martrewes/CompleteLightsOutProject/ArduinoCode/src/levels.h

char Level1[25] = {'0', '0', '0', '0', '0', '0', '0', '0', '0', '0', '0', '0', '0', '0', '0', '1', '0', '1', '0', '1', '1', '0', '1', '0', '1'};
char Level2[25] = {'1', '0', '1', '0', '1', '1', '0', '1', '0', '1', '0', '0', '0', '0', '0', '1', '0', '1', '0', '1', '1', '0', '1', '0', '1'};
char Level3[25] = {'0', '1', '0', '1', '0', '1', '1', '0', '1', '1', '1', '1', '0', '1', '1', '1', '1', '0', '1', '1', '0', '1', '0', '1', '0'};
char Level4[25] = {'0', '0', '0', '0', '0', '1', '1', '0', '1', '1', '0', '0', '0', '0', '0', '1', '0', '0', '0', '1', '1', '1', '0', '1', '1'};
char Level5[25] = {'1', '1', '1', '1', '0', '1', '1', '1', '0', '1', '1', '1', '1', '0', '1', '0', '0', '0', '1', '1', '1', '1', '0', '1', '1'};
char Level6[25] = {'0', '0', '0', '0', '0', '0', '0', '0', '0', '0', '1', '0', '1', '0', '1', '1', '0', '1', '0', '1', '0', '1', '1', '1', '0'};
char Level7[25] = {'1', '1', '1', '1', '0', '1', '0', '0', '0', '1', '1', '0', '0', '0', '1', '1', '0', '0', '0', '1', '1', '1', '1', '1', '0'};
char Level8[25] = {'0', '0', '0', '0', '0', '0', '0', '1', '0', '0', '0', '1', '0', '1', '0', '1', '0', '1', '0', '1', '0', '1', '0', '1', '0'};
char Level9[25] = {'0', '1', '0', '1', '0', '1', '1', '1', '1', '1', '0', '1', '1', '1', '0', '0', '1', '0', '1', '1', '1', '1', '1', '0', '0'};
char Level10[25] = {'0', '1', '1', '1', '0', '0', '1', '1', '1', '0', '0', '1', '1', '1', '0', '0', '0', '0', '0', '0', '0', '0', '0', '0', '0'};
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
char HLevel29[25] = {'2', '1', '2', '0', '0', '2', '2', '2', '1', '0', '1', '0', '2', '0', '1', '0', '1', '2', '2', '2', '0', '0', '2', '1', '2'};
char HLevel30[25] = {'0', '0', '2', '0', '0', '1', '0', '1', '0', '1', '2', '1', '2', '1', '2', '1', '0', '1', '0', '1', '0', '0', '2', '0', '0'};
char HLevel31[25] = {'0', '2', '0', '0', '2', '2', '2', '1', '1', '0', '0', '1', '1', '1', '0', '0', '1', '1', '2', '2', '2', '0', '0', '2', '0'};
char HLevel32[25] = {'0', '1', '1', '1', '0', '0', '0', '0', '0', '0', '2', '0', '2', '0', '2', '0', '0', '0', '0', '0', '2', '0', '2', '0', '2'};
char HLevel33[25] = {'0', '1', '1', '1', '0', '0', '0', '0', '0', '0', '1', '0', '0', '0', '1', '0', '0', '0', '0', '0', '2', '0', '2', '0', '2'};
char HLevel34[25] = {'0', '2', '1', '2', '2', '0', '2', '2', '1', '2', '0', '1', '0', '0', '2', '0', '0', '0', '1', '2', '0', '0', '2', '1', '2'};
char HLevel35[25] = {'1', '2', '0', '2', '1', '1', '2', '0', '2', '1', '1', '2', '1', '2', '1', '1', '2', '0', '2', '1', '1', '2', '0', '2', '1'};
char HLevel36[25] = {'0', '0', '0', '0', '0', '1', '0', '2', '0', '1', '1', '0', '1', '0', '1', '1', '0', '2', '0', '1', '0', '0', '0', '0', '0'};
char HLevel37[25] = {'2', '2', '0', '2', '2', '0', '1', '2', '0', '0', '0', '2', '1', '1', '2', '2', '2', '1', '1', '2', '0', '2', '0', '2', '0'};
char HLevel38[25] = {'2', '1', '2', '0', '0', '2', '2', '1', '1', '0', '1', '2', '1', '2', '1', '0', '1', '1', '2', '2', '0', '0', '2', '1', '2'};
char HLevel39[25] = {'0', '0', '1', '0', '0', '0', '0', '1', '0', '0', '0', '0', '0', '0', '0', '0', '0', '2', '0', '0', '0', '0', '2', '0', '0'};
char HLevel40[25] = {'0', '0', '1', '0', '0', '0', '1', '1', '1', '0', '2', '2', '2', '2', '2', '1', '2', '2', '2', '1', '1', '1', '2', '1', '1'};
char HLevel41[25] = {'1', '0', '2', '0', '1', '0', '0', '0', '0', '0', '2', '0', '1', '0', '2', '0', '0', '0', '0', '0', '1', '0', '2', '0', '1'};
char HLevel42[25] = {'2', '0', '1', '0', '2', '0', '0', '2', '0', '0', '1', '2', '1', '2', '1', '0', '0', '2', '0', '0', '2', '0', '1', '0', '2'};
char HLevel43[25] = {'0', '0', '0', '0', '0', '0', '2', '0', '0', '0', '0', '0', '2', '0', '0', '0', '2', '0', '0', '0', '0', '0', '0', '0', '0'};
char HLevel44[25] = {'1', '1', '1', '2', '1', '1', '1', '1', '0', '1', '1', '0', '1', '1', '0', '1', '2', '2', '0', '1', '2', '0', '0', '0', '1'};
char HLevel45[25] = {'2', '2', '1', '2', '1', '1', '2', '2', '0', '1', '2', '1', '2', '2', '0', '2', '2', '1', '0', '1', '2', '2', '2', '0', '1'};
char HLevel46[25] = {'2', '1', '1', '1', '2', '1', '2', '1', '2', '1', '1', '1', '2', '1', '1', '1', '2', '1', '2', '1', '2', '1', '1', '1', '2'};
char HLevel47[25] = {'0', '0', '2', '0', '0', '0', '2', '2', '1', '0', '0', '0', '0', '2', '2', '2', '1', '2', '0', '2', '1', '1', '0', '1', '1'};
char HLevel48[25] = {'0', '0', '0', '0', '0', '1', '0', '2', '0', '1', '2', '0', '2', '0', '2', '1', '0', '2', '0', '1', '0', '0', '0', '0', '0'};
char HLevel49[25] = {'0', '2', '0', '0', '0', '0', '2', '0', '0', '0', '0', '0', '1', '0', '0', '0', '0', '0', '2', '2', '2', '0', '0', '0', '0'};
char HLevel50[25] = {'0', '2', '2', '2', '0', '0', '2', '1', '2', '0', '0', '2', '2', '2', '0', '0', '2', '2', '2', '0', '0', '0', '0', '0', '0'};

char XHLevel1[25] = {'0', '0', '2', '0', '0', '1', '0', '0', '0', '1', '1', '0', '2', '0', '1', '1', '0', '0', '0', '1', '0', '0', '2', '0', '0'};
char XHLevel2[25] = {'2', '0', '2', '0', '2', '0', '0', '0', '0', '0', '2', '0', '1', '0', '2', '0', '0', '0', '0', '0', '2', '0', '2', '0', '2'};
char XHLevel3[25] = {'0', '2', '2', '2', '0', '0', '2', '2', '2', '0', '2', '1', '1', '1', '2', '2', '1', '1', '1', '2', '2', '1', '1', '1', '2'};
char XHLevel4[25] = {'1', '0', '0', '0', '1', '2', '0', '0', '0', '2', '2', '0', '0', '0', '2', '2', '0', '0', '0', '2', '1', '0', '0', '0', '1'};
char XHLevel5[25] = {'0', '1', '0', '1', '0', '0', '0', '0', '0', '0', '1', '0', '0', '0', '1', '0', '2', '2', '2', '0', '0', '0', '2', '0', '0'};
char XHLevel6[25] = {'2', '0', '2', '0', '2', '0', '0', '0', '0', '0', '2', '0', '2', '0', '2', '0', '0', '0', '0', '0', '2', '0', '2', '0', '2'};
char XHLevel7[25] = {'2', '1', '1', '1', '2', '2', '1', '1', '1', '2', '2', '1', '1', '1', '2', '2', '1', '1', '1', '2', '2', '1', '1', '1', '2'};
char XHLevel8[25] = {'0', '0', '0', '0', '0', '0', '0', '0', '0', '0', '0', '2', '1', '2', '0', '0', '0', '0', '0', '0', '0', '0', '0', '0', '0'};
char XHLevel9[25] = {'0', '0', '2', '0', '0', '1', '1', '0', '1', '1', '0', '0', '0', '0', '0', '0', '0', '2', '0', '0', '0', '0', '0', '0', '0'};
char XHLevel10[25] = {'0', '0', '0', '0', '0', '0', '0', '0', '0', '0', '1', '0', '0', '0', '1', '0', '0', '0', '0', '0', '0', '0', '0', '0', '0'};
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
char XHLevel39[25] = {'1', '0', '1', '0', '1', '0', '1', '1', '1', '0', '0', '0', '2', '0', '0', '0', '0', '0', '0', '0', '1', '0', '0', '0', '1'};
char XHLevel40[25] = {'1', '1', '0', '2', '2', '1', '1', '0', '2', '2', '1', '1', '1', '1', '1', '1', '1', '1', '2', '2', '1', '1', '1', '2', '2'};
char XHLevel41[25] = {'0', '0', '0', '0', '0', '1', '0', '0', '0', '1', '1', '0', '0', '0', '1', '1', '0', '0', '0', '1', '0', '0', '0', '0', '0'};
char XHLevel42[25] = {'1', '1', '1', '0', '0', '1', '0', '0', '0', '0', '1', '1', '0', '0', '0', '1', '0', '0', '0', '0', '1', '1', '1', '0', '0'};
char XHLevel43[25] = {'2', '1', '2', '1', '2', '1', '2', '1', '2', '1', '2', '1', '0', '1', '2', '1', '2', '1', '2', '1', '2', '1', '2', '1', '2'};
char XHLevel44[25] = {'1', '2', '2', '2', '1', '2', '0', '2', '1', '1', '2', '0', '0', '2', '1', '1', '2', '1', '1', '2', '2', '2', '0', '2', '2'};
char XHLevel45[25] = {'1', '2', '1', '2', '1', '1', '0', '1', '0', '1', '1', '0', '1', '0', '1', '1', '1', '1', '1', '1', '1', '0', '1', '0', '1'};
char XHLevel46[25] = {'0', '0', '1', '1', '1', '0', '0', '2', '0', '2', '2', '1', '2', '2', '0', '0', '1', '2', '0', '1', '0', '1', '0', '0', '2'};
char XHLevel47[25] = {'1', '1', '2', '0', '0', '0', '1', '2', '2', '1', '1', '0', '0', '0', '1', '2', '2', '0', '2', '1', '1', '2', '1', '1', '0'};
char XHLevel48[25] = {'1', '0', '1', '0', '0', '1', '0', '0', '1', '0', '2', '2', '1', '2', '0', '1', '0', '0', '2', '1', '2', '2', '1', '1', '0'};
char XHLevel49[25] = {'1', '1', '2', '1', '1', '0', '1', '2', '1', '0', '1', '0', '2', '0', '1', '0', '1', '1', '1', '0', '1', '0', '1', '0', '1'};
char XHLevel50[25] = {'2', '0', '1', '0', '2', '1', '2', '1', '2', '1', '1', '0', '2', '0', '1', '0', '0', '0', '0', '0', '1', '0', '0', '0', '1'};

char menuLeds[25] = {'0', '1', '0', '1', '0', '1', '0', '0', '0', '1', '0', '1', '0', '1', '0', '0', '0', '0', '0', '0', '0', '2', '2', '2', '0'};

// 'bg', 128x32px
const unsigned char bgImage [] PROGMEM = {
    0xff, 0xff, 0xff, 0xff, 0xff, 0xff, 0xff, 0xff, 0xff, 0xff, 0xff, 0xff, 0xff, 0xff, 0xff, 0xff, 
    0x80, 0x00, 0x00, 0x00, 0x00, 0x00, 0x00, 0x00, 0xc0, 0x00, 0x00, 0x00, 0x00, 0x00, 0x00, 0x01, 
    0xa0, 0x00, 0x04, 0x00, 0x00, 0x00, 0x00, 0x00, 0xd1, 0x00, 0x00, 0x00, 0x00, 0x00, 0x00, 0x01, 
    0xa1, 0x92, 0x64, 0x00, 0x00, 0x00, 0x00, 0x00, 0xdb, 0x32, 0x4c, 0x70, 0x00, 0x00, 0x00, 0x01, 
    0xa2, 0xd2, 0xb4, 0x00, 0x00, 0x00, 0x00, 0x00, 0xd5, 0x4a, 0x56, 0xc0, 0x00, 0x00, 0x00, 0x01, 
    0xa3, 0x14, 0xc4, 0x00, 0x00, 0x00, 0x00, 0x00, 0xd1, 0x4a, 0x98, 0x30, 0x00, 0x00, 0x00, 0x01, 
    0xb9, 0x88, 0x64, 0x00, 0x00, 0x00, 0x00, 0x00, 0xd1, 0x31, 0x0c, 0xe0, 0x00, 0x00, 0x00, 0x01, 
    0x80, 0x00, 0x00, 0x00, 0x00, 0x00, 0x00, 0x00, 0xc0, 0x00, 0x00, 0x00, 0x00, 0x00, 0x00, 0x01, 
    0x80, 0x00, 0x00, 0x00, 0x00, 0x00, 0x00, 0x00, 0xc0, 0x00, 0x00, 0x00, 0x00, 0x00, 0x00, 0x01, 
    0x80, 0x00, 0x00, 0x00, 0x00, 0x00, 0x00, 0x00, 0xc0, 0x00, 0x00, 0x00, 0x00, 0x00, 0x00, 0x01, 
    0x80, 0x00, 0x00, 0x00, 0x00, 0x00, 0x00, 0x00, 0xc0, 0x00, 0x00, 0x00, 0x00, 0x00, 0x00, 0x01, 
    0x80, 0x00, 0x00, 0x00, 0x00, 0x00, 0x00, 0x00, 0xc0, 0x00, 0x00, 0x00, 0x00, 0x00, 0x00, 0x01, 
    0x80, 0x00, 0x00, 0x00, 0x00, 0x00, 0x00, 0x00, 0xc0, 0x00, 0x00, 0x00, 0x00, 0x00, 0x00, 0x01, 
    0x80, 0x00, 0x00, 0x00, 0x00, 0x00, 0x00, 0x00, 0xc0, 0x00, 0x00, 0x00, 0x00, 0x00, 0x00, 0x01, 
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
	0x80, 0x00, 0x00, 0x00, 0x00, 0x00, 0x00, 0x00, 0x00, 0x00, 0x00, 0x00, 0x00, 0x00, 0x00, 0x01, 
	0x80, 0x00, 0x00, 0x00, 0x00, 0x00, 0x00, 0x00, 0x00, 0x00, 0x00, 0x00, 0x00, 0x00, 0x00, 0x01, 
	0x80, 0x00, 0x00, 0x00, 0x00, 0x00, 0x00, 0x00, 0x00, 0x00, 0x00, 0x00, 0x00, 0x00, 0x00, 0x01, 
	0x80, 0x00, 0x00, 0x00, 0x00, 0x00, 0x00, 0x00, 0x00, 0x00, 0x00, 0x00, 0x00, 0x00, 0x00, 0x01, 
	0x80, 0x00, 0x00, 0x00, 0x00, 0x00, 0x00, 0x00, 0x00, 0x00, 0x00, 0x00, 0x00, 0x00, 0x00, 0x01, 
	0x80, 0x00, 0x00, 0x00, 0x00, 0x00, 0x00, 0x00, 0x00, 0x00, 0x00, 0x00, 0x00, 0x00, 0x00, 0x01, 
	0x80, 0x00, 0x00, 0x00, 0x00, 0x00, 0x00, 0x00, 0x00, 0x00, 0x00, 0x00, 0x00, 0x00, 0x00, 0x01, 
	0x80, 0x00, 0x00, 0x00, 0x00, 0x00, 0x00, 0x00, 0x00, 0x00, 0x00, 0x00, 0x00, 0x00, 0x00, 0x01, 
	0xff, 0xff, 0xff, 0xff, 0xff, 0xff, 0xff, 0xff, 0xff, 0xff, 0xff, 0xff, 0xff, 0xff, 0xff, 0xff
};
